nekuneko/SimuRain/Documentación/Fotos/IMG_20181212_210646_184.jpg

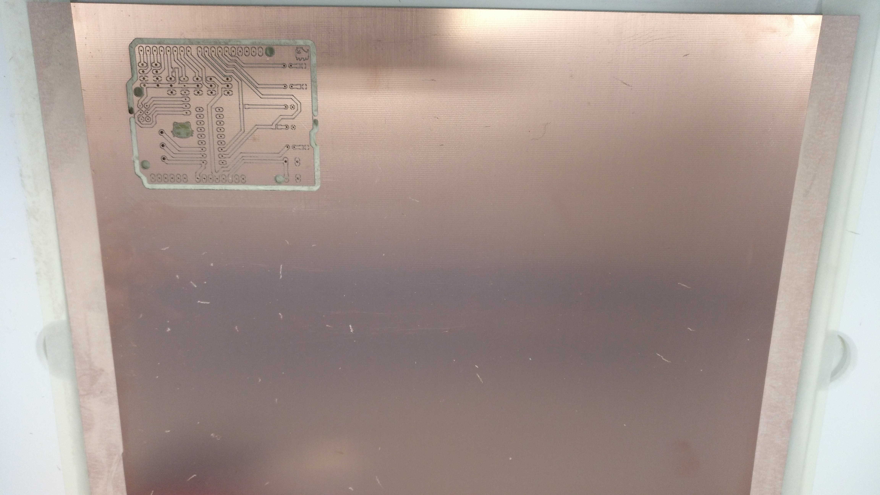
Documentación/Fotos/IMG_20181212_210646_184.jpg
