nekuneko/SimuRain/Documentación/Fotos/IMG_20181212_210701_623.jpg

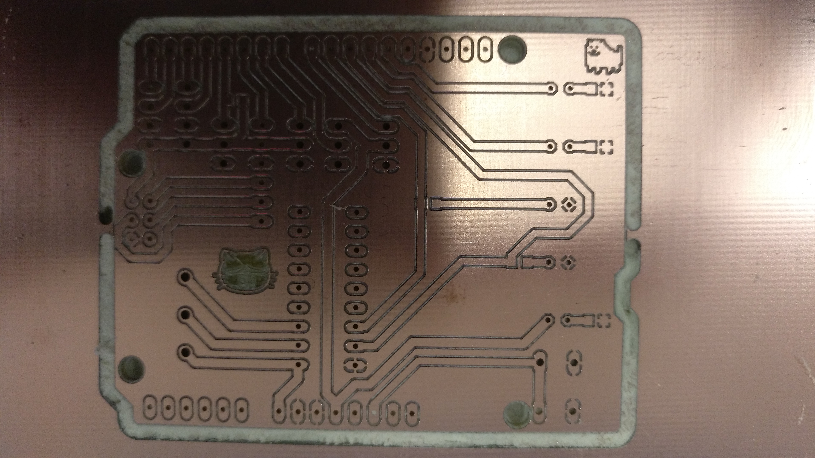
Documentación/Fotos/IMG_20181212_210701_623.jpg
