nekuneko/SimuRain/Documentación/Fotos/IMG_20181212_230549_840.jpg

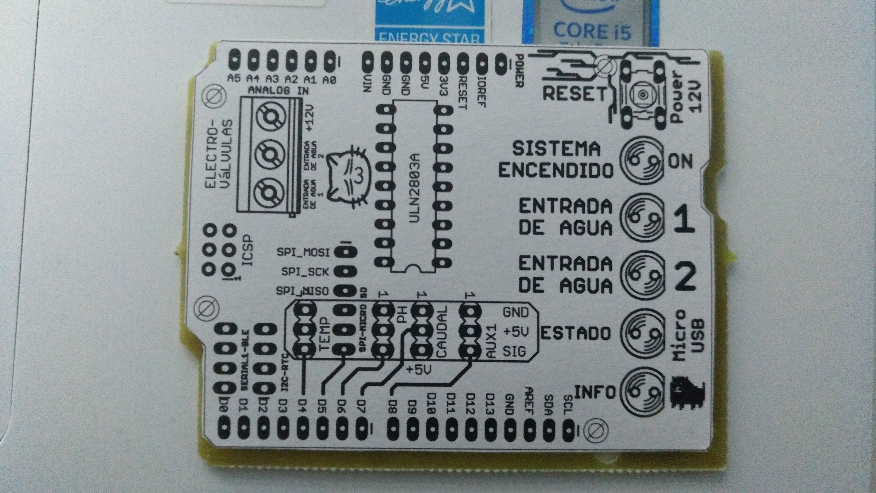
Documentación/Fotos/IMG_20181212_230549_840.jpg
