nekuneko/SimuRain/Documentación/Fotos/IMG_20181212_230841_363.jpg

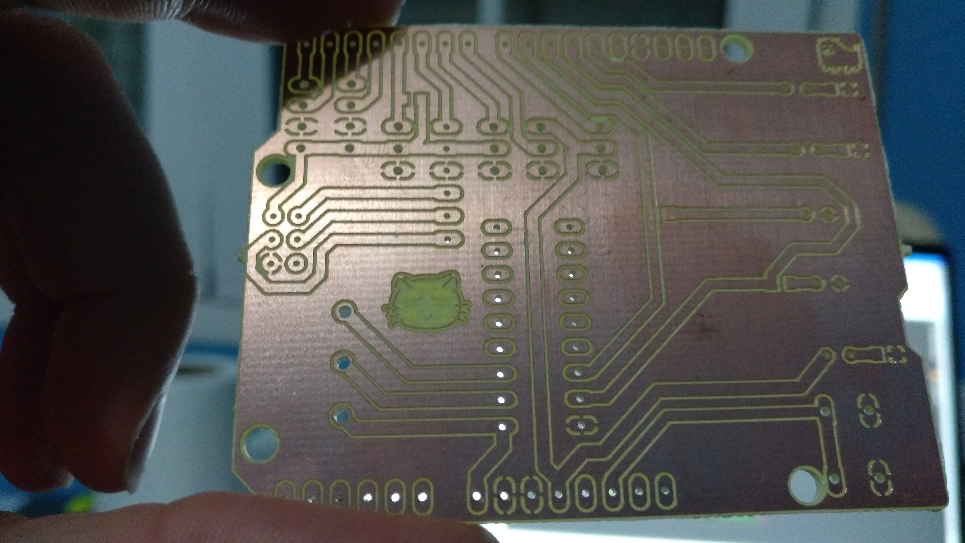
Documentación/Fotos/IMG_20181212_230841_363.jpg
