nekuneko/SimuRain/Documentación/Fotos/IMG_20181212_230850_781.jpg

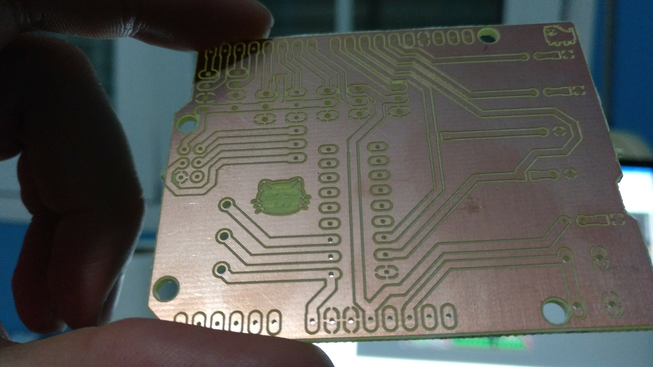
Documentación/Fotos/IMG_20181212_230850_781.jpg
