nekuneko/SimuRain/Documentación/Fotos/IMG_20181212_230857_860.jpg

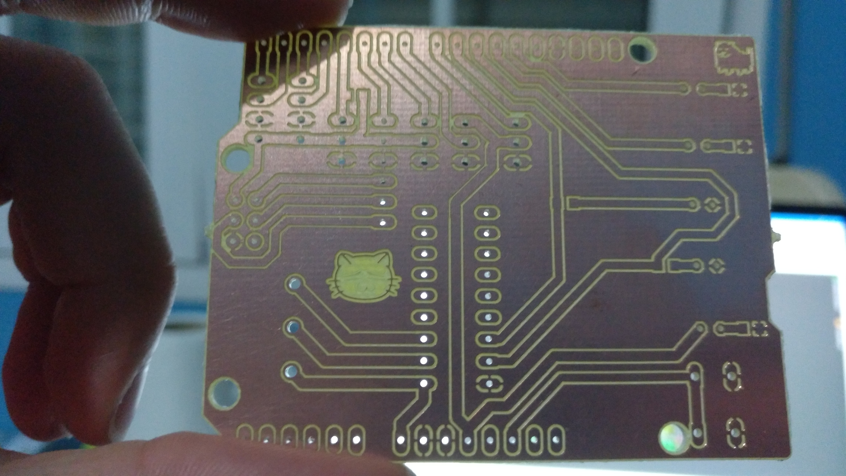
Documentación/Fotos/IMG_20181212_230857_860.jpg
